celso/NMS3000/schematics/NMS3000.kicad_pcb

## EAGLE design ardnanoplcdemo/NANOEveryV3.0.sch

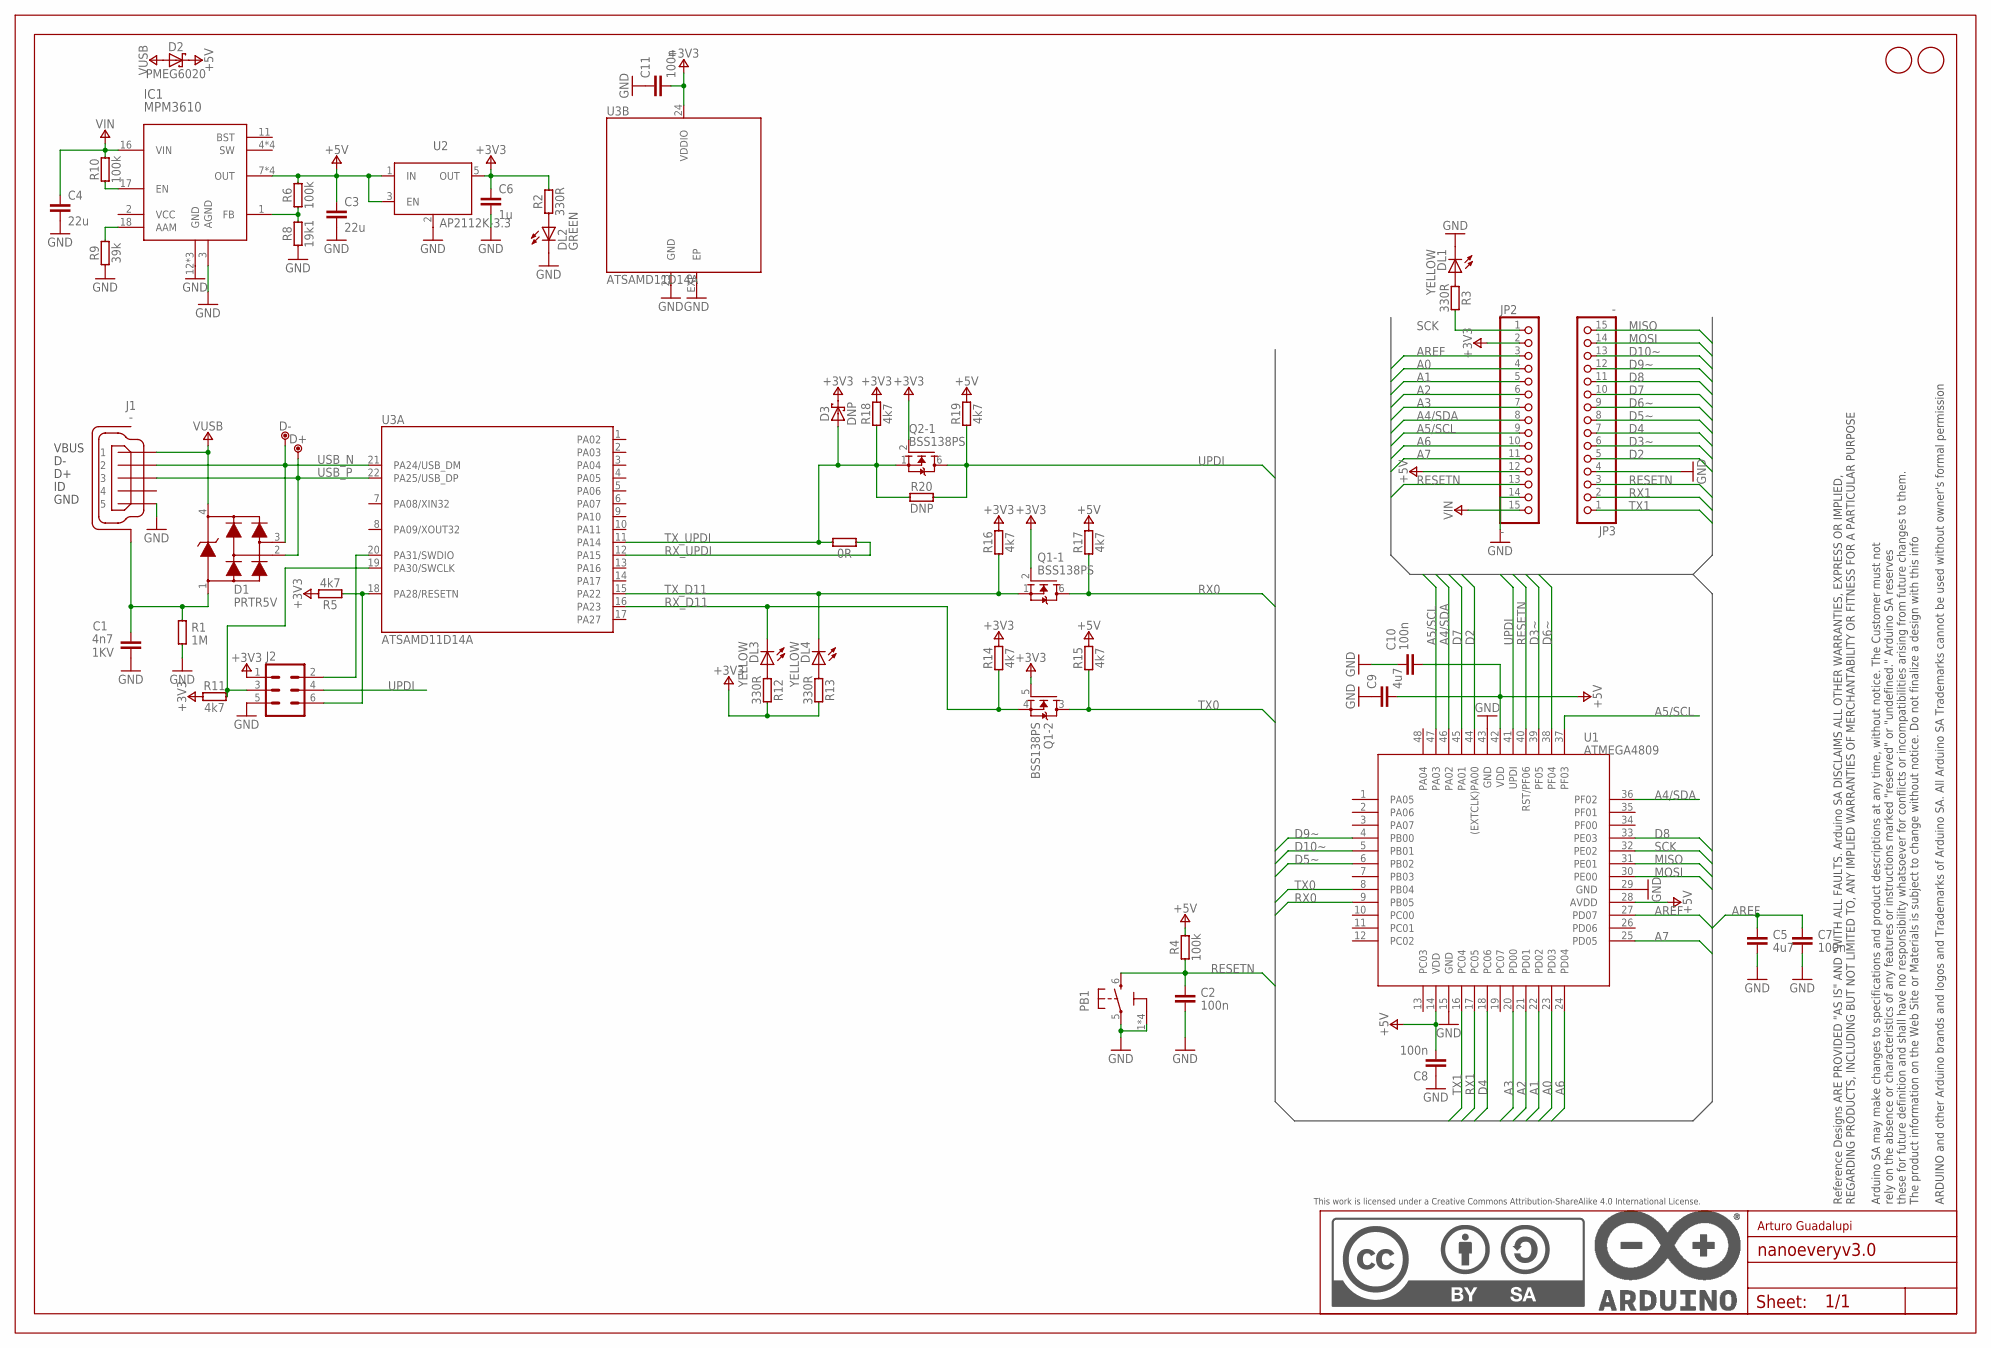
[picture p2: schematic NANOEveryV3.0.sch]

Parts:
C1: 4n7; 0805-R2013X50N; VOLTAGE 1KV
C2, C7, C8, C10, C11: 100n; 0402-1005X55N
C3, C4: 22u; 0805-R2013X50N
C5, C9: 4u7; 0402-1005X55N
C6: 1u; 0402-1005X55N
D1: PRTR5V; SOT190P230X110-4N
D2: PMEG6020; SODFL3517X110N
D3: DNP; SODFL3517X110N
D+: DNP; TP-1.00MM
D-: DNP; TP-1.00MM
DL1, DL3, DL4: YELLOW; LEDC1608X80N-AK
DL2: GREEN; LEDC1608X80N-AK
FD1, FD2: DNP; FD-1-1.5
FRAME1: DNP; FRAME
IC1: MPM3610
J1: -; ZX62-AB-5PA
J2: DNP; 2X03-TP
JP2, JP3: -; 1X15-CASTELL
PB1: PTS820; C&K_PTS820_NO_HOLES
Q1, Q2: BSS138PS; SOT363
R1: 1M; 0402-1005X55N
R2, R3, R12, R13: 330R; 0402-1005X55N
R4, R6, R10: 100k; 0402-1005X55N
R5, R11, R14, R15, R16, R17, R18, R19: 4k7; 0402-1005X55N
R7: 0R; 0402-1005X55N
R8: 19k1; 0402-1005X55N
R9: 39k; 0402-1005X55N
R20: DNP; 0402-1005X55N
U1: ATMEGA4809; TQFP48
U2: AP2112K-3.3; SOT25
U3: ATSAMD11D14A; HVQFN24

Connections:
+3V3: C6.1, C11.2, D3.C, J2.1, JP2.2, Q1.2 (G), Q1.5 (G), Q2.2 (G), R2.2, R5.2, R11.1, R12.2, R13.2, R14.2, R16.2, R18.2, U2.5 (OUT), U3.24 (VDDIO)
+5V: C3.1, C8.2, C9.2, C10.2, D2.C, IC1.7 (OUT), JP2.12, R4.2, R6.2, R15.2, R17.2, R19.2, U1.14 (VDD), U1.28 (AVDD), U1.42 (VDD), U2.1 (IN), U2.3 (EN)
A0: JP2.4, U1.23 (PD03)
A1: JP2.5, U1.22 (PD02)
A2: JP2.6, U1.21 (PD01)
A3: JP2.7, U1.20 (PD00)
A4/SDA: JP2.8, U1.36 (PF02), U1.46 (PA02)
A5/SCL: JP2.9, U1.37 (PF03), U1.47 (PA03)
A6: JP2.10, U1.24 (PD04)
A7: JP2.11, U1.25 (PD05)
AREF: C5.1, C7.1, JP2.3, U1.27 (PD07)
D2: JP3.5, U1.44 ((EXTCLK)PA00)
D3~: JP3.6, U1.39 (PF05)
D4: JP3.7, U1.18 (PC06)
D5~: JP3.8, U1.6 (PB02)
D6~: JP3.9, U1.38 (PF04)
D7: JP3.10, U1.45 (PA01)
D8: JP3.11, U1.33 (PE03)
D9~: JP3.12, U1.4 (PB00)
D10~: JP3.13, U1.5 (PB01)
D11_RESET: J2.6, R5.1, U3.18 (PA28/RESETN)
D11_SWCLK: J2.3, R11.2, U3.19 (PA30/SWCLK)
D11_SWDIO: J2.2, U3.20 (PA31/SWDIO)
GND: C1.2, C2.2, C3.2, C4.2, C5.2, C6.2, C7.2, C8.1, C9.1, C10.1, C11.1, DL1.C, DL2.C, IC1.3 (AGND), IC1.12 (GND), J1.5, J2.5, JP2.14, JP3.4, PB1.1 (3), PB1.5 (1), R1.1, R8.1, R9.1, U1.15 (GND), U1.29 (GND), U1.43 (GND), U2.2 (GND/ADJ), U3.23 (GND), U3.EXP (EP)
MISO: JP3.15, U1.31 (PE01)
MOSI: JP3.14, U1.30 (PE00)
unnamed: C1.1, D1.1, J1.6 (SH), R1.2
unnamed: DL2.A, R2.1
unnamed: DL1.A, R3.1
unnamed: IC1.1 (FB), R6.1, R8.2
unnamed: IC1.18 (AAM), R9.2
unnamed: IC1.17 (EN), R10.1
unnamed: DL3.A, R12.1
unnamed: DL4.A, R13.1
RESETN: C2.1, JP2.13, JP3.3, PB1.6 (2), R4.1, U1.40 (RST/PF06)
RX0: Q1.6 (D), R17.1, U1.9 (PB05)
RX1: JP3.2, U1.17 (PC05)
RX_D11: DL3.C, Q1.4 (S), R14.1, U3.16 (PA23)
RX_UPDI: R7.2, U3.12 (PA15)
SCK: JP2.1, R3.2, U1.32 (PE02)
TX0: Q1.3 (D), R15.1, U1.8 (PB04)
TX1: JP3.1, U1.16 (PC04)
TX_D11: DL4.C, Q1.1 (S), R16.1, U3.15 (PA22)
TX_UPDI: D3.A, Q2.1 (S), R7.1, R18.1, R20.1, U3.11 (PA14)
UPDI: J2.4, Q2.6 (D), R19.1, R20.2, U1.41 (UPDI)
USB_N: D1.3, D-.X, J1.2, U3.21 (PA24/USB_DM)
USB_P: D1.2, D+.X, J1.3, U3.22 (PA25/USB_DP)
VIN: C4.1, IC1.16 (VIN), JP2.15, R10.2
VUSB: D1.4, D2.A, J1.1

Notes on the sheet:
Arturo Guadalupi
