celso/NMS3000/schematics/NMS3000.kicad_pcb

## KiCad design ardnanoplcdemo/ardnanoplcdemo.kicad_sch

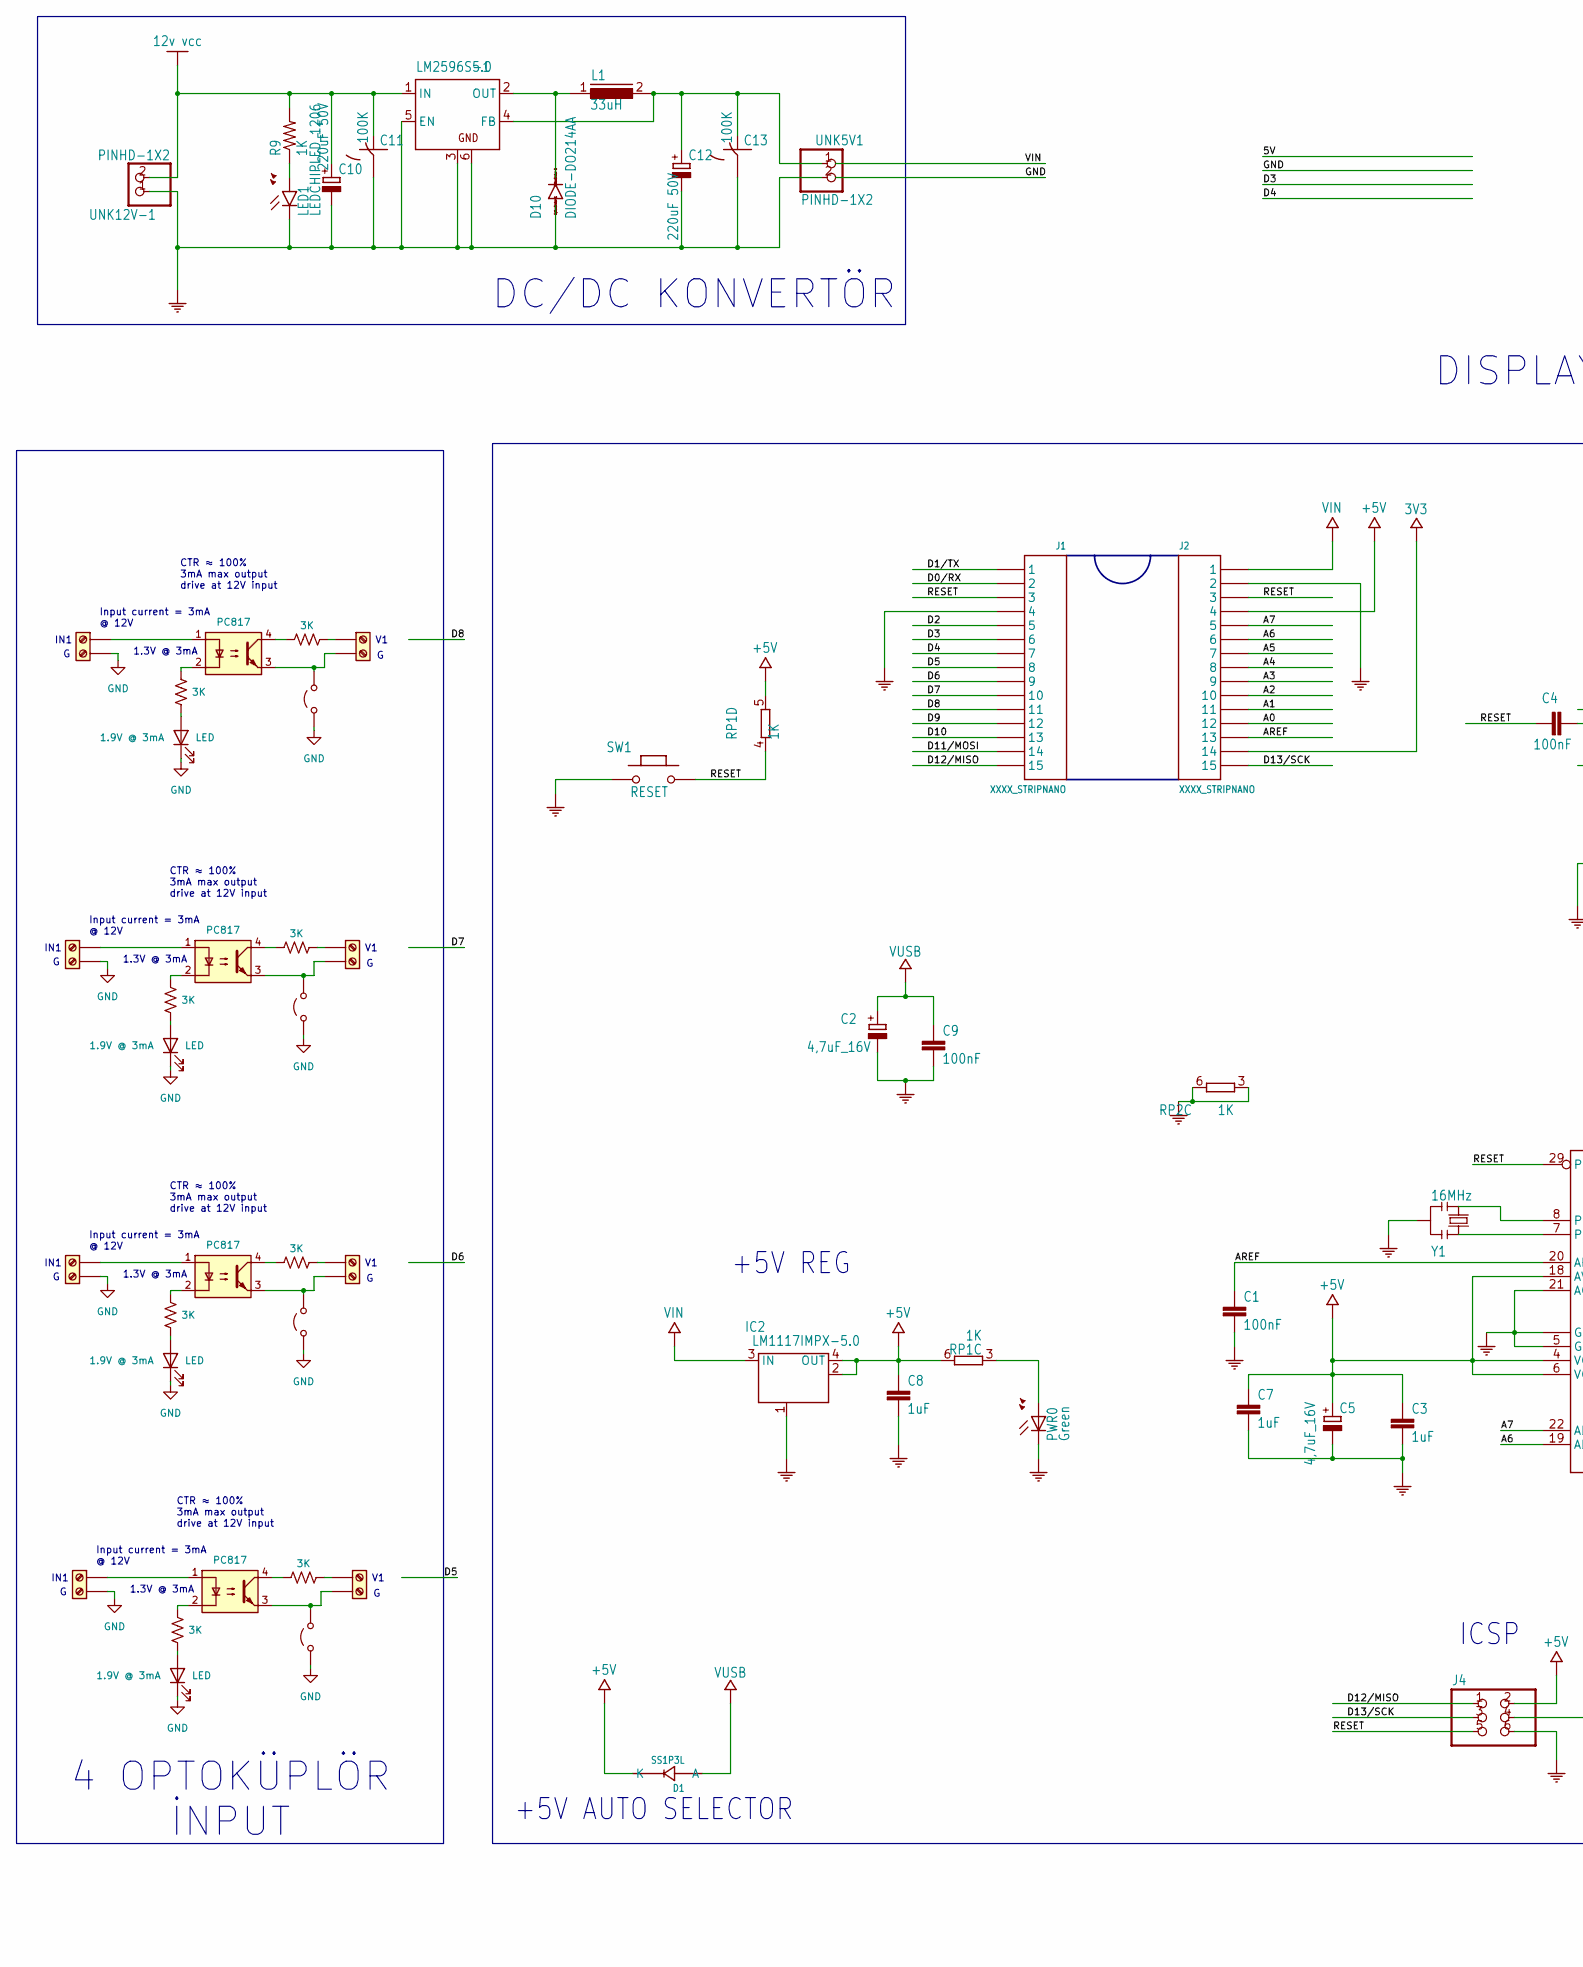
[picture p4: schematic ardnanoplcdemo.kicad_sch, part in row 1, column 1]

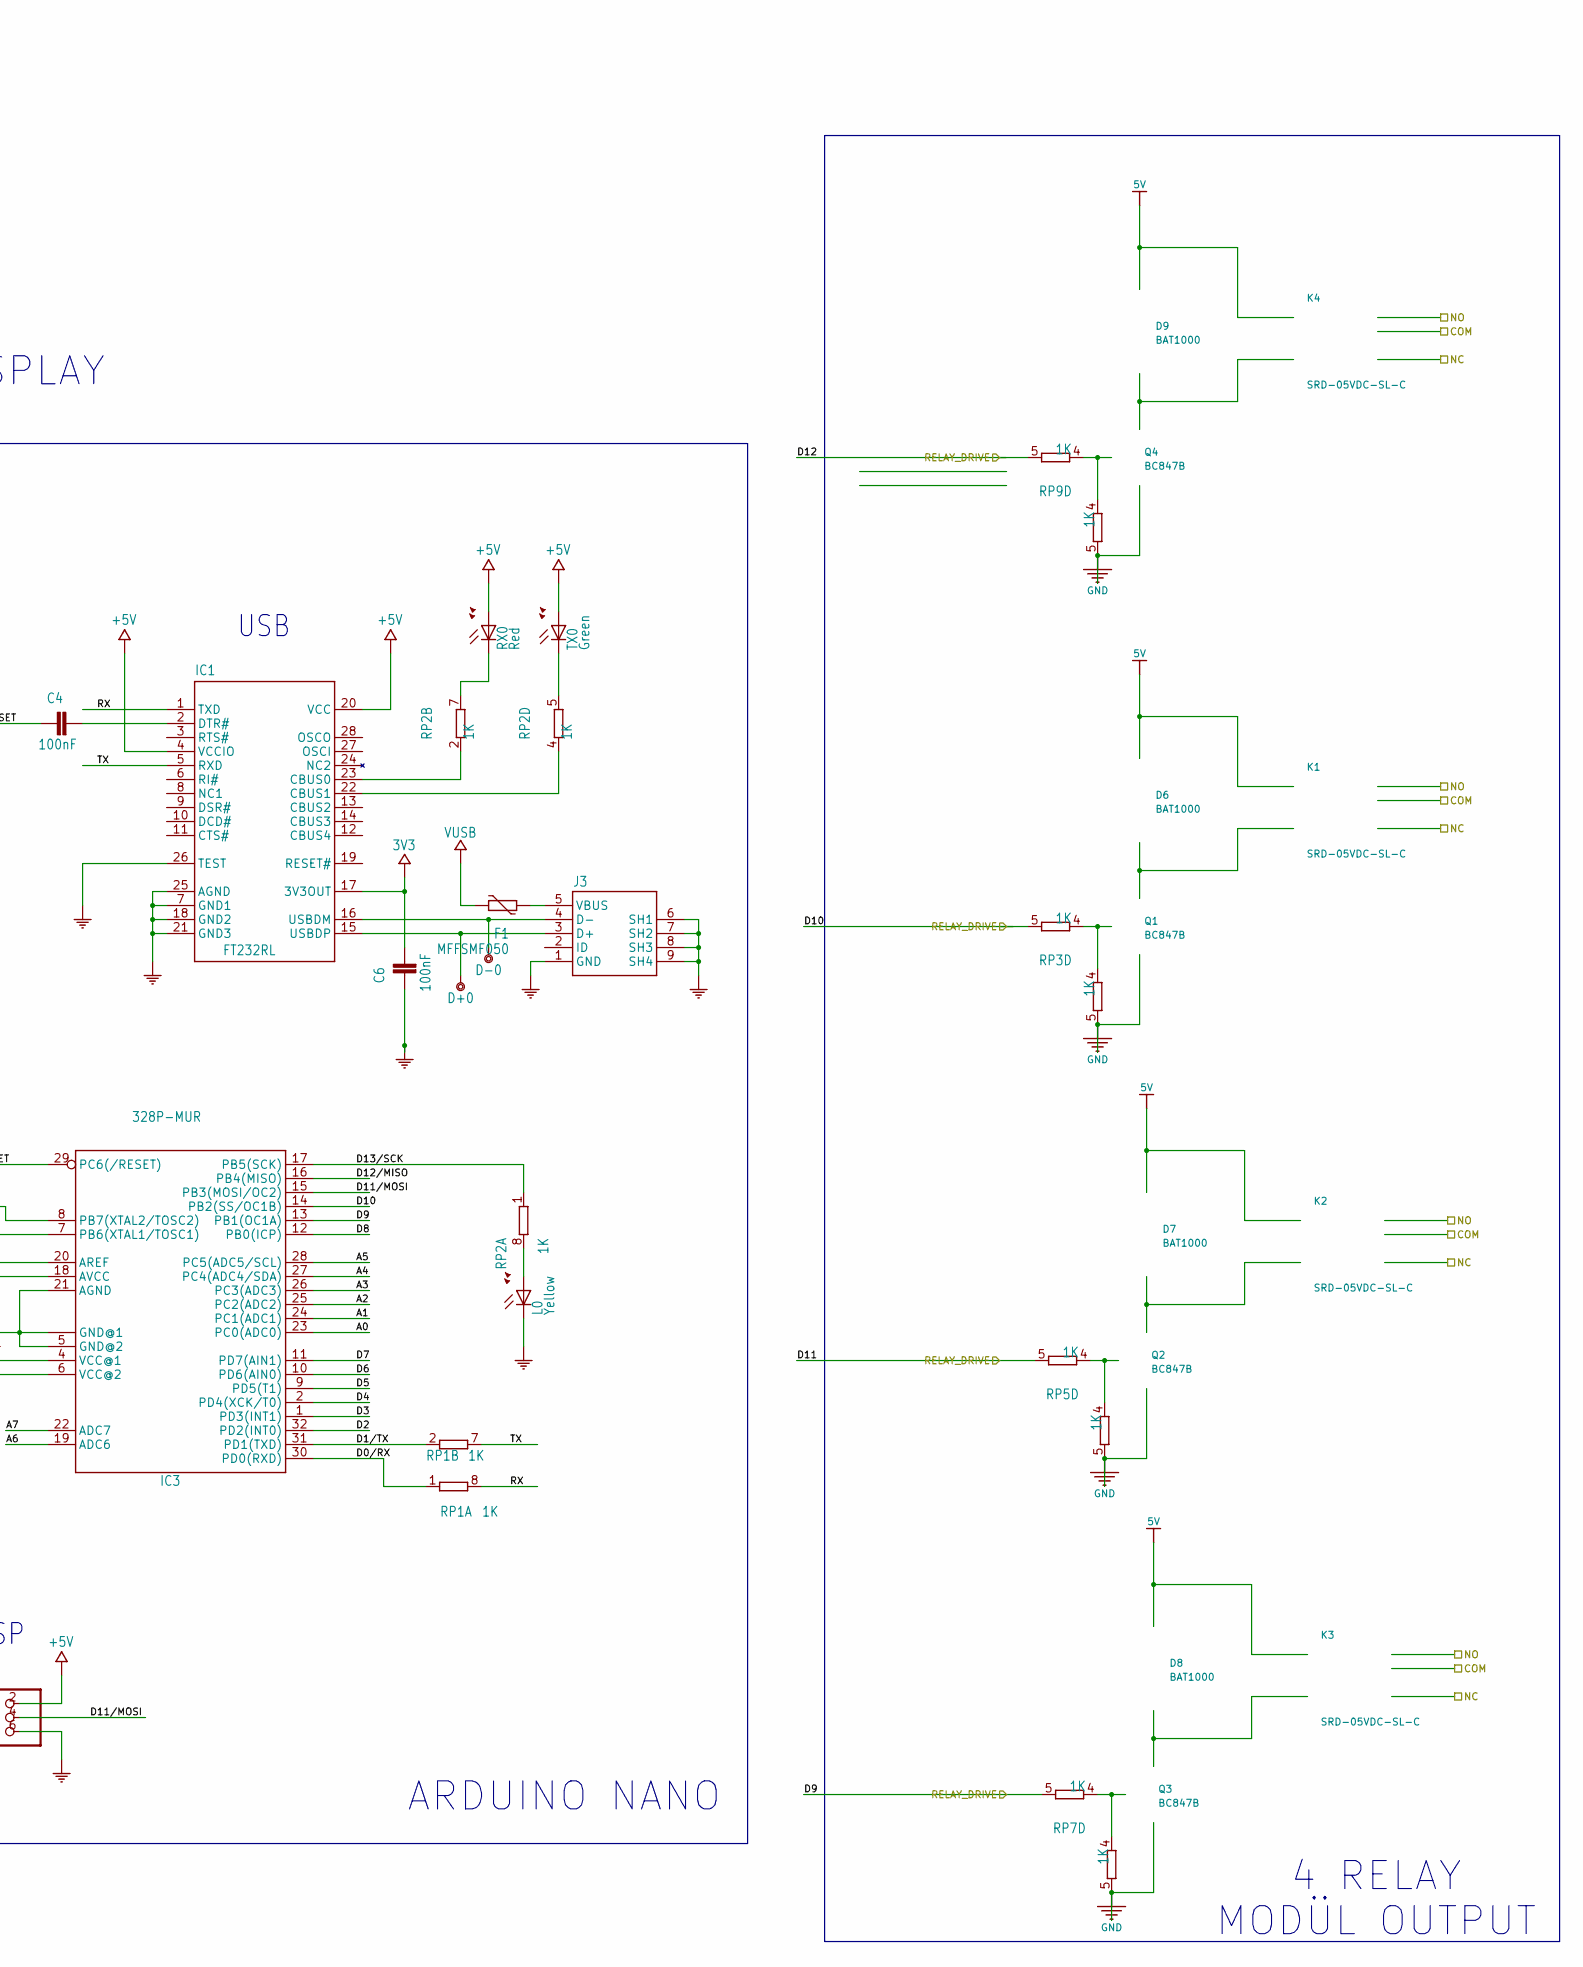
[picture p5: schematic ardnanoplcdemo.kicad_sch, part in row 1, column 2]

Parts:
C1, C4, C6, C9: 100nF; C0603-ROUND
C2, C5: 4,7uF_16V; TAN-A
C3, C7, C8: 1uF; C0603-ROUND
C10, C12: 220uF 50V; CAPAE1030X1050N
C11, C13: 100K; CAPC3216X135
D1: SS1P3L; DO220AAL
D2, D3, D4, D5: LED
D6, D7, D8, D9: BAT1000; SOT91P240X110-3N
D10: DIODE-DO214AA; DO214AA
D+0: DNP; TP-1.00MM
D-0: DNP; TP-1.00MM
F1: MFFSMF050; 0603-1608X90N
IC1: FT232RL; SSOP28
IC2: LM1117IMPX-5.0; LINEAR_SOT223
IC3: 328P-MUR; VQFN32
J1, J2: XXXX_STRIPNANO; HEAD15-NOSS
J3: 0219_14850; USB-MINI-B_2
J4: 0114_PH254-203DF118A00V; 2X03
J5, J6, J7, J8, J9, J10, J11, J12: Screw_Terminal_01x02
JP1, JP2, JP3, JP4: Jumper_2_Open
K1, K2, K3, K4: SRD-05VDC-SL-C; RELAY_SRD-05VDC-SL-C
L0: Yellow; CHIPLED_0805
L1: 33uH; SRR1210
LED1: LEDCHIPLED_1206; CHIPLED_1206
LM2596S-1: 5.0; TO263-5
PWR0: Green; CHIPLED_0805
Q1, Q2, Q3, Q4: BC847B; SOT100P230X110-3N
R1, R2, R3, R4, R5, R6, R7, R8: 3K
R9: 1K; R1206
RP1, RP2, RP3, RP4, RP5, RP6, RP7, RP8, RP9, RP10: 1K; CAY16
RX0: Red; CHIPLED_0805
SW1: RESET; SMD_157SW
TX0: Green; CHIPLED_0805
U1, U2, U3, U4: PC817; DIP-4_W7.62mm
UNK5V1, UNK12V-1: PINHD-1X2; 1X02
Y1: 16MHz; RESONATOR

Connections:
3V3: C6.2, IC1.17 (3V3OUT), J2.14
12v vcc: C10.1 (+), C11.1, LM2596S-1.1 (IN), R9.2, UNK12V-1.2
+5V: C3.1, C5.1 (+), C7.1, C8.1, D1.P$1 (K), IC1.4 (VCCIO), IC1.20 (VCC), IC2.2 (OUT@1), IC2.4 (OUT), IC3.4 (VCC@1), IC3.6 (VCC@2), IC3.18 (AVCC), J2.4, J4.2, RP1.5 (2), RP1.6 (2), RX0.A, TX0.A
A0: IC3.23 (PC0(ADC0)), J2.12
A1: IC3.24 (PC1(ADC1)), J2.11
A2: IC3.25 (PC2(ADC2)), J2.10
A3: IC3.26 (PC3(ADC3)), J2.9
A4: IC3.27 (PC4(ADC4/SDA)), J2.8
A5: IC3.28 (PC5(ADC5/SCL)), J2.7
A6: IC3.19 (ADC6), J2.6
A7: IC3.22 (ADC7), J2.5
AREF: C1.1, IC3.20 (AREF), J2.13
COM: C1.2, C2.2 (-), C3.2, C5.2 (-), C6.1, C7.2, C8.2, C9.2, C10.2 (-), C11.2, C12.2 (-), C13.2, D10.A, IC1.7 (GND1), IC1.18 (GND2), IC1.21 (GND3), IC1.25 (AGND), IC1.26 (TEST), IC2.1 (GND/ADJ), IC3.3 (GND@1), IC3.5 (GND@2), IC3.21 (AGND), IC3.33 (GND@1), J1.4, J2.2, J3.1 (GND), J3.6 (SH1), J3.7 (SH2), J3.8 (SH3), J3.9 (SH4), J4.6, L0.C, LED1.C, LM2596S-1.3 (GND), LM2596S-1.5 (EN), LM2596S-1.6 (GND@1), PWR0.C, RP2.3 (1), RP2.6 (2), SW1.1, UNK5V1.2, UNK12V-1.1, Y1.2
D0/RX: IC3.30 (PD0(RXD)), J1.2, RP1.1
D1/TX: IC3.31 (PD1(TXD)), J1.1, RP1.2 (1)
D2: IC3.32 (PD2(INT0)), J1.5
D3: IC3.1 (PD3(INT1)), J1.6
D4: IC3.2 (PD4(XCK/T0)), J1.7
D5: IC3.9 (PD5(T1)), J1.8
D6: IC3.10 (PD6(AIN0)), J1.9
D7: IC3.11 (PD7(AIN1)), J1.10
D8: IC3.12 (PB0(ICP)), J1.11
D10: IC3.13 (PB1(OC1A)), IC3.14 (PB2(SS/OC1B)), J1.12, J1.13, RP3.5 (2), RP5.5 (2), RP7.5 (2), RP9.5 (2)
D11/MOSI: IC3.15 (PB3(MOSI/OC2)), J1.14, J4.4
D12/MISO: IC3.16 (PB4(MISO)), J1.15, J4.1
D13/SCK: IC3.17 (PB5(SCK)), J2.15, J4.3, RP2.1
GND: D2.1 (K), D3.1 (K), D4.1 (K), D5.1 (K), J5.2, J7.2, J9.2, J11.2, JP1.1 (A), JP2.1 (A), JP3.1 (A), JP4.1 (A), RP4.5 (2), RP6.5 (2), RP8.5 (2), RP10.5 (2)
unnamed: C4.2, IC1.2 (DTR#)
unnamed: C12.1 (+), C13.1, L1.2, LM2596S-1.4 (FB), UNK5V1.1
unnamed: D2.2 (A), R1.2
unnamed: D3.2 (A), R3.2
unnamed: D4.2 (A), R5.2
unnamed: D5.2 (A), R7.2
unnamed: D10.C, L1.1, LM2596S-1.2 (OUT)
unnamed: D+0.X, IC1.15 (USBDP), J3.3 (D+)
unnamed: D-0.X, IC1.16 (USBDM), J3.4 (D-)
unnamed: F1.2, J3.5 (VBUS)
unnamed: IC1.22 (CBUS1), RP2.4 (1)
unnamed: IC1.23 (CBUS0), RP2.2 (1)
unnamed: IC3.7 (PB6(XTAL1/TOSC1)), Y1.1
unnamed: IC3.8 (PB7(XTAL2/TOSC2)), Y1.3
unnamed: J5.1, U1.1
unnamed: J6.1, R2.1
unnamed: J6.2, JP1.2 (B), U1.3
unnamed: J7.1, U2.1
unnamed: J8.1, R4.1
unnamed: J8.2, JP2.2 (B), U2.3
unnamed: J9.1, U3.1
unnamed: J10.1, R6.1
unnamed: J10.2, JP3.2 (B), U3.3
unnamed: J11.1, U4.1
unnamed: J12.1, R8.1
unnamed: J12.2, JP4.2 (B), U4.3
unnamed: L0.A, RP2.8 (2)
unnamed: LED1.A, R9.1
unnamed: PWR0.A, RP1.3 (1)
unnamed: R1.1, U1.2
unnamed: R2.2, U1.4
unnamed: R3.1, U2.2
unnamed: R4.2, U2.4
unnamed: R5.1, U3.2
unnamed: R6.2, U3.4
unnamed: R7.1, U4.2
unnamed: R8.2, U4.4
unnamed: RP2.5 (2), TX0.C
unnamed: RP2.7 (2), RX0.C
unnamed: RP3.4 (1), RP4.4 (1)
unnamed: RP5.4 (1), RP6.4 (1)
unnamed: RP7.4 (1), RP8.4 (1)
unnamed: RP9.4 (1), RP10.4 (1)
RESET: C4.1, IC3.29 (PC6(/RESET)), J1.3, J2.3, J4.5, RP1.4 (1), SW1.2
RX: IC1.1 (TXD), RP1.8 (2)
TX: IC1.5 (RXD), RP1.7 (2)
VIN: IC2.3 (IN), J2.1
VUSB: C2.1 (+), C9.1, D1.P$2 (A), F1.1

Notes on the sheet:
DC/DC KONVERTÖR
4 RELAY MODÜL OUTPUT
1.3V @ 3mA
CTR ≈ 100% 3mA max output drive at 12V input
DISPLAY
+5V AUTO SELECTOR
IN1
ICSP
Input current = 3mA @ 12V
USB
ARDUINO NANO
+5V REG
4 OPTOKÜPLÖR İNPUT
