celso/NMS3000/schematics/NMS3000.kicad_pcb

## KiCad design ardnanoplcdemo/ardnanoplcdemo.kicadv1_sch.kicad_sch

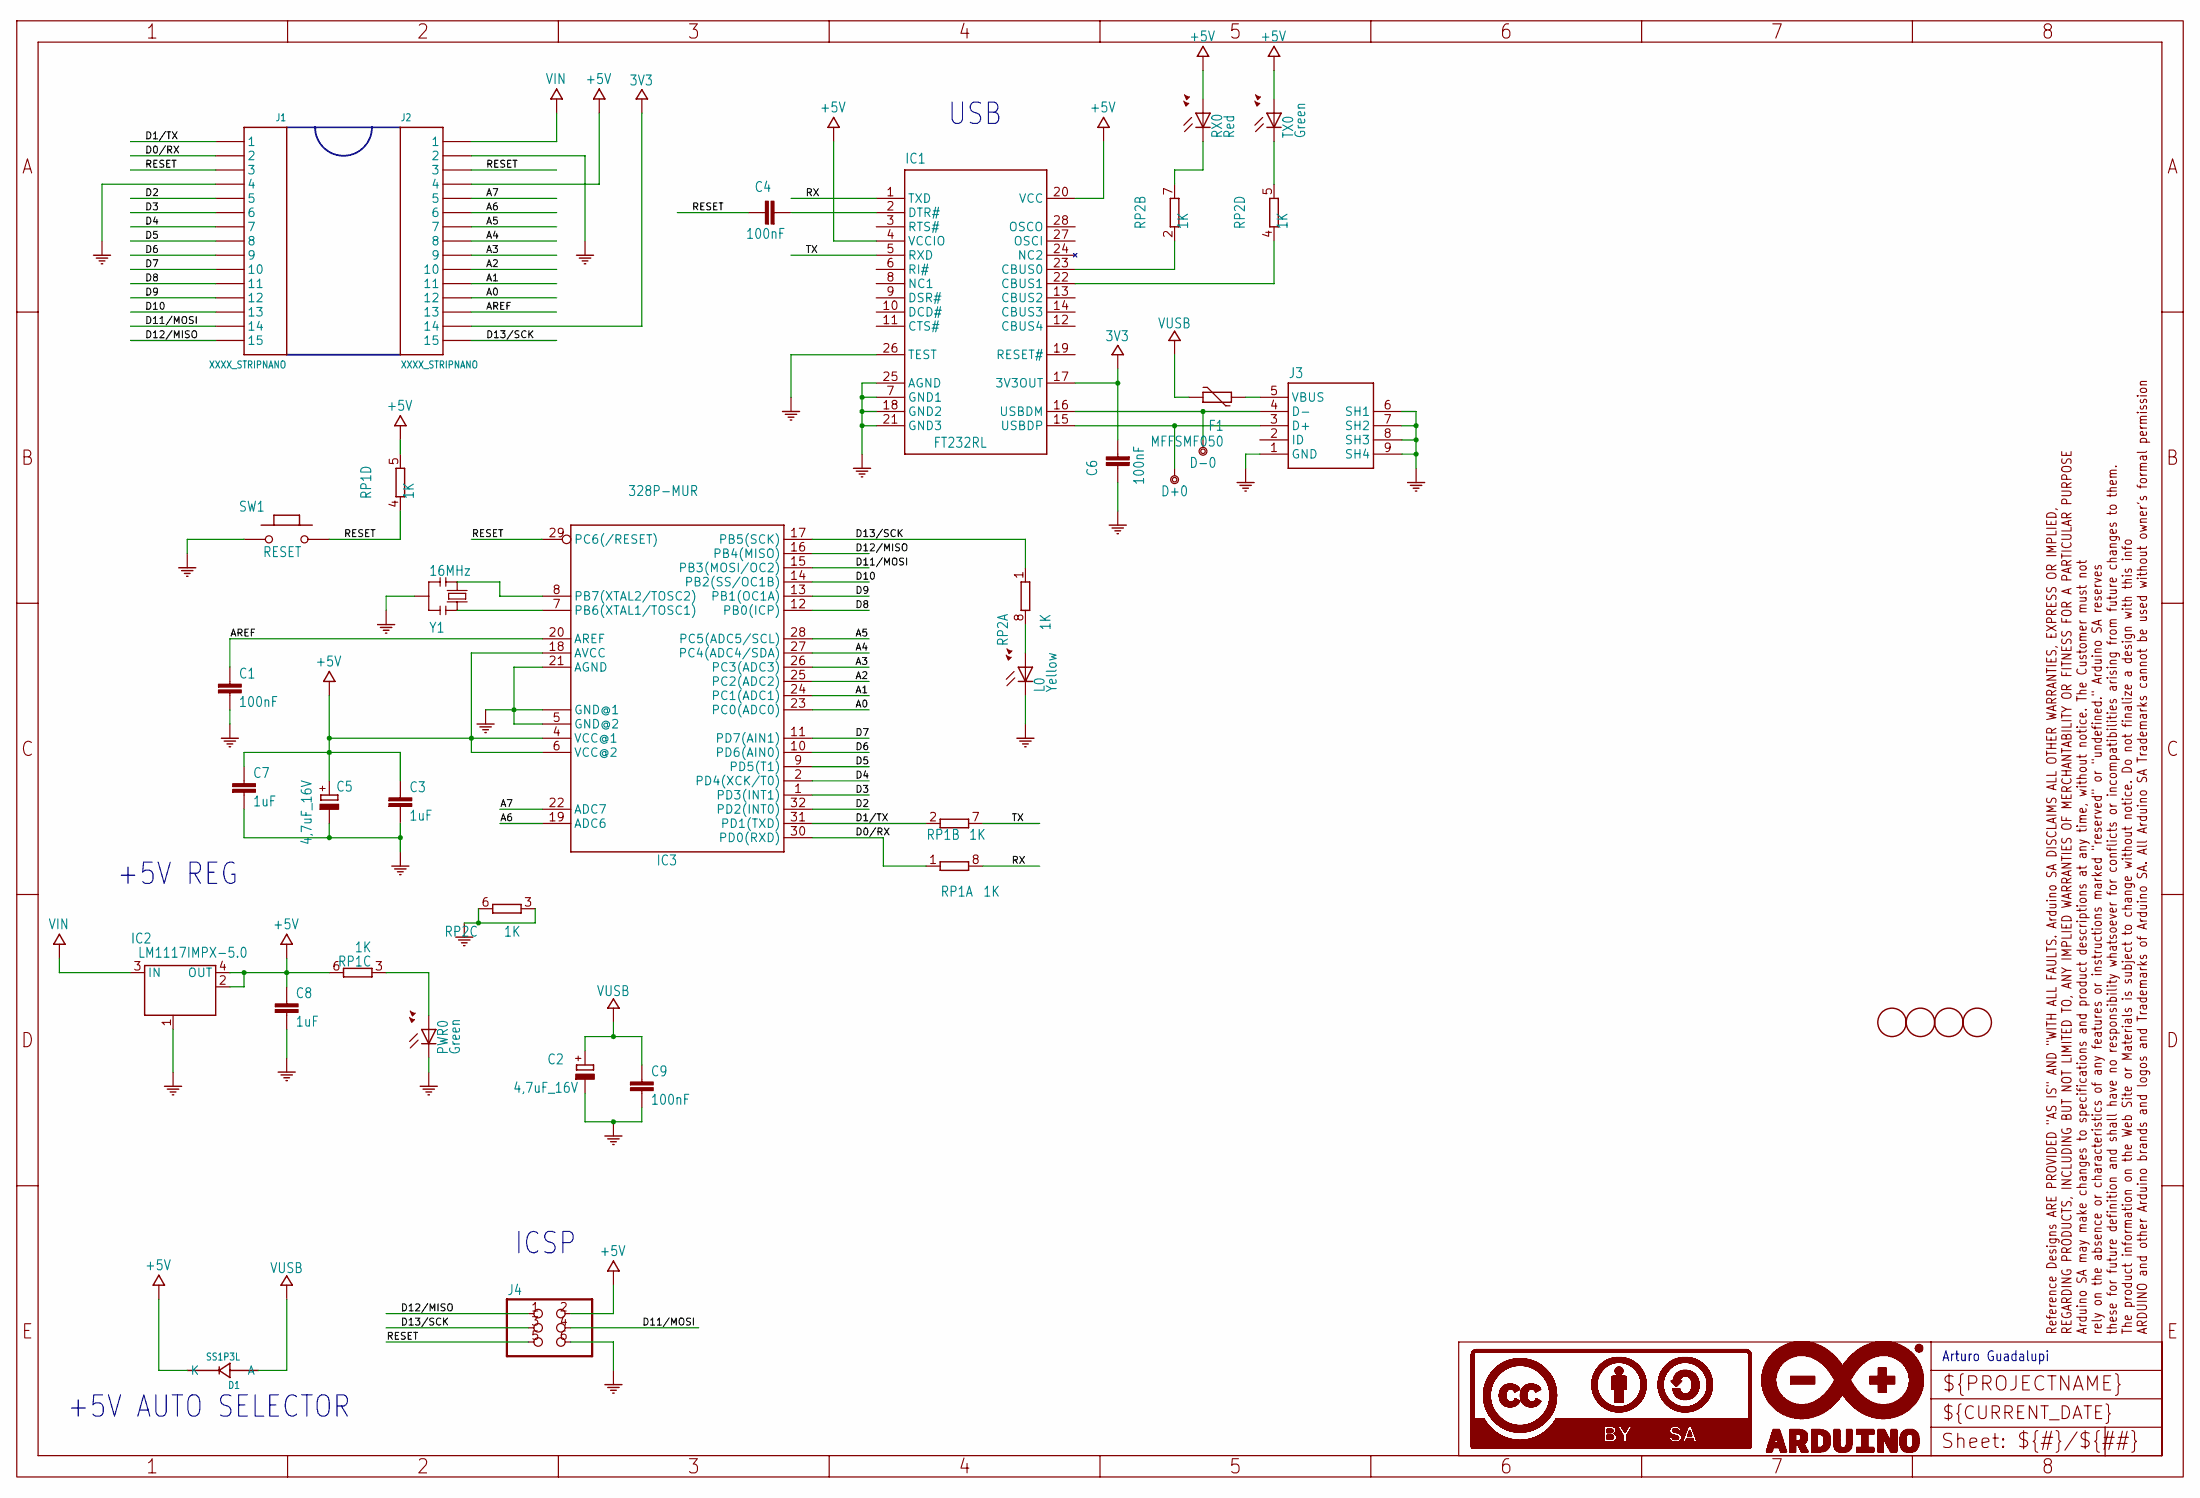
[picture p6: schematic ardnanoplcdemo.kicadv1_sch.kicad_sch]

Parts:
C1, C4, C6, C9: 100nF; C0603-ROUND
C2, C5: 4,7uF_16V; TAN-A
C3, C7, C8: 1uF; C0603-ROUND
D1: SS1P3L; DO220AAL
D+0: DNP; TP-1.00MM
D-0: DNP; TP-1.00MM
F1: MFFSMF050; 0603-1608X90N
FRAME1: DNP; FRAME
IC1: FT232RL; SSOP28
IC2: LM1117IMPX-5.0; LINEAR_SOT223
IC3: 328P-MUR; VQFN32
J1, J2: XXXX_STRIPNANO; HEAD15-NOSS
J3: 0219_14850; USB-MINI-B_2
J4: 0114_PH254-203DF118A00V; 2X03
L0: Yellow; CHIPLED_0805
PWR0: Green; CHIPLED_0805
RP1, RP2: 1K; CAY16
RX0: Red; CHIPLED_0805
SW1: RESET; SMD_157SW
TX0: Green; CHIPLED_0805
U$4, U$5, U$53, U$54: DNP; FD-1-1.5
Y1: 16MHz; RESONATOR

Connections:
3V3: C6.2, IC1.17 (3V3OUT), J2.14
+5V: C3.1, C5.1 (+), C7.1, C8.1, D1.P$1 (K), IC1.4 (VCCIO), IC1.20 (VCC), IC2.2 (OUT@1), IC2.4 (OUT), IC3.4 (VCC@1), IC3.6 (VCC@2), IC3.18 (AVCC), J2.4, J4.2, RP1.5 (2), RP1.6 (2), RX0.A, TX0.A
A0: IC3.23 (PC0(ADC0)), J2.12
A1: IC3.24 (PC1(ADC1)), J2.11
A2: IC3.25 (PC2(ADC2)), J2.10
A3: IC3.26 (PC3(ADC3)), J2.9
A4: IC3.27 (PC4(ADC4/SDA)), J2.8
A5: IC3.28 (PC5(ADC5/SCL)), J2.7
A6: IC3.19 (ADC6), J2.6
A7: IC3.22 (ADC7), J2.5
AREF: C1.1, IC3.20 (AREF), J2.13
COM: C1.2, C2.2 (-), C3.2, C5.2 (-), C6.1, C7.2, C8.2, C9.2, IC1.7 (GND1), IC1.18 (GND2), IC1.21 (GND3), IC1.25 (AGND), IC1.26 (TEST), IC2.1 (GND/ADJ), IC3.3 (GND@1), IC3.5 (GND@2), IC3.21 (AGND), IC3.33 (GND@1), J1.4, J2.2, J3.1 (GND), J3.6 (SH1), J3.7 (SH2), J3.8 (SH3), J3.9 (SH4), J4.6, L0.C, PWR0.C, RP2.3 (1), RP2.6 (2), SW1.1, Y1.2
D0/RX: IC3.30 (PD0(RXD)), J1.2, RP1.1
D1/TX: IC3.31 (PD1(TXD)), J1.1, RP1.2 (1)
D2: IC3.32 (PD2(INT0)), J1.5
D3: IC3.1 (PD3(INT1)), J1.6
D4: IC3.2 (PD4(XCK/T0)), J1.7
D5: IC3.9 (PD5(T1)), J1.8
D6: IC3.10 (PD6(AIN0)), J1.9
D7: IC3.11 (PD7(AIN1)), J1.10
D8: IC3.12 (PB0(ICP)), J1.11
D9: IC3.13 (PB1(OC1A)), J1.12
D10: IC3.14 (PB2(SS/OC1B)), J1.13
D11/MOSI: IC3.15 (PB3(MOSI/OC2)), J1.14, J4.4
D12/MISO: IC3.16 (PB4(MISO)), J1.15, J4.1
D13/SCK: IC3.17 (PB5(SCK)), J2.15, J4.3, RP2.1
unnamed: C4.2, IC1.2 (DTR#)
unnamed: D+0.X, IC1.15 (USBDP), J3.3 (D+)
unnamed: D-0.X, IC1.16 (USBDM), J3.4 (D-)
unnamed: F1.2, J3.5 (VBUS)
unnamed: IC1.22 (CBUS1), RP2.4 (1)
unnamed: IC1.23 (CBUS0), RP2.2 (1)
unnamed: IC3.7 (PB6(XTAL1/TOSC1)), Y1.1
unnamed: IC3.8 (PB7(XTAL2/TOSC2)), Y1.3
unnamed: L0.A, RP2.8 (2)
unnamed: PWR0.A, RP1.3 (1)
unnamed: RP2.5 (2), TX0.C
unnamed: RP2.7 (2), RX0.C
RESET: C4.1, IC3.29 (PC6(/RESET)), J1.3, J2.3, J4.5, RP1.4 (1), SW1.2
RX: IC1.1 (TXD), RP1.8 (2)
TX: IC1.5 (RXD), RP1.7 (2)
VIN: IC2.3 (IN), J2.1
VUSB: C2.1 (+), C9.1, D1.P$2 (A), F1.1

Notes on the sheet:
+5V AUTO SELECTOR
ICSP
USB
Arturo Guadalupi
+5V REG
